jvasilakes/mito/pics/1000009353.jpg

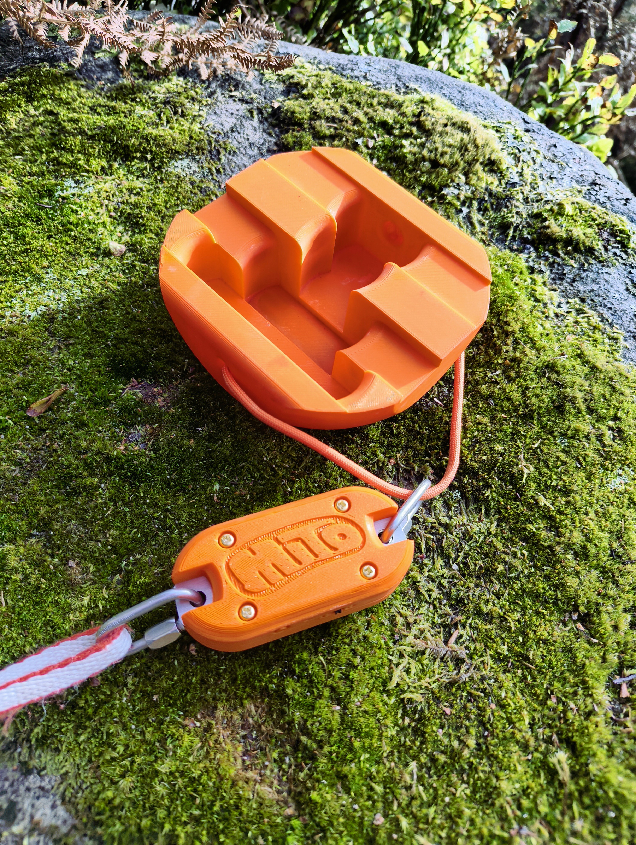
pics/1000009353.jpg
