jvasilakes/mito/pics/1000009354.jpg

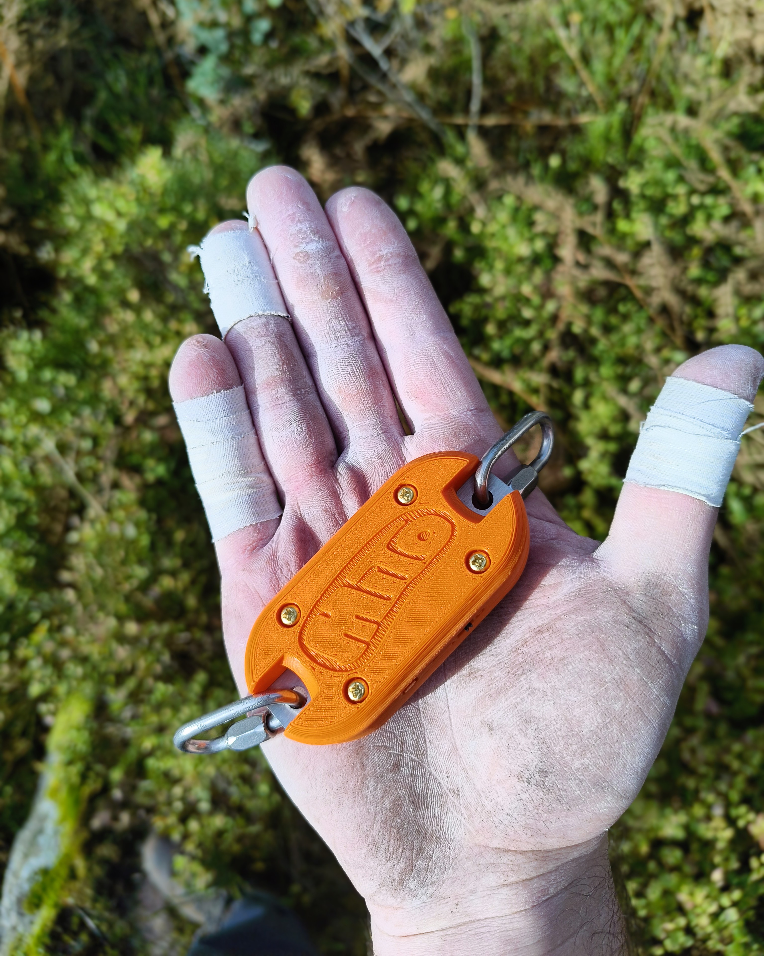
pics/1000009354.jpg
