jvasilakes/mito/pics/1000009355.png

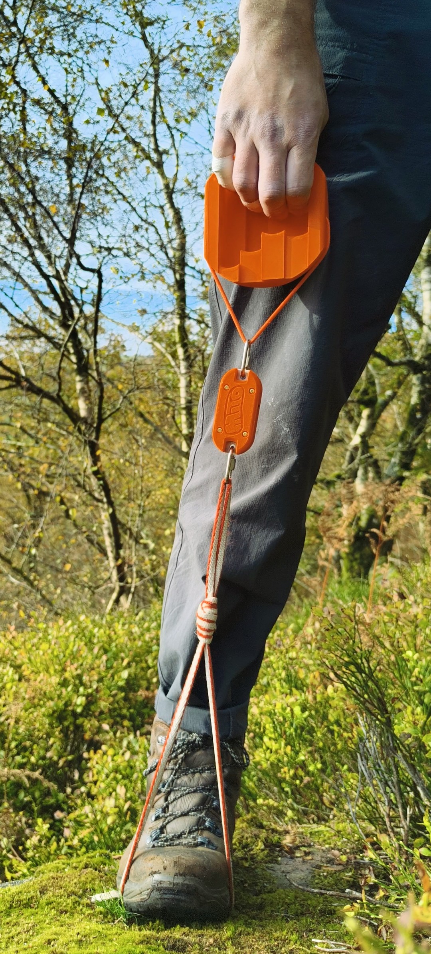
pics/1000009355.png
