jvasilakes/mito/hardware/enclosure/enclosure_bottom_with_window.3mf

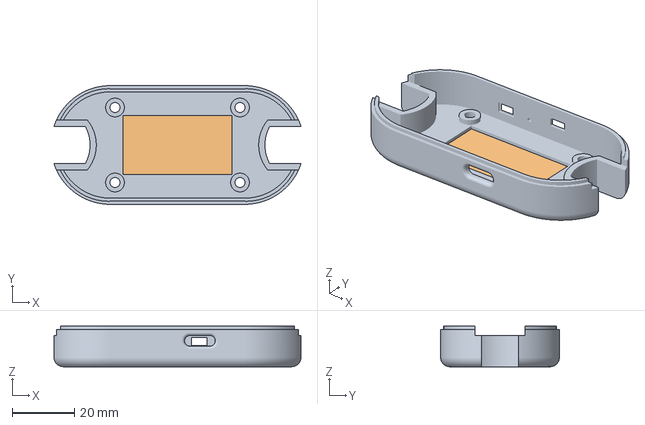
[picture p23: CAD file, 2025-10-13]
hardware/enclosure/enclosure_bottom_with_window.3mf
79.1 x 38.0 x 13.0 mm
enclosure2-Bottom_with_window.step
enclosure2-Bottom_window.step
