jvasilakes/mito/hardware/enclosure/enclosure2-Bottom_window.step

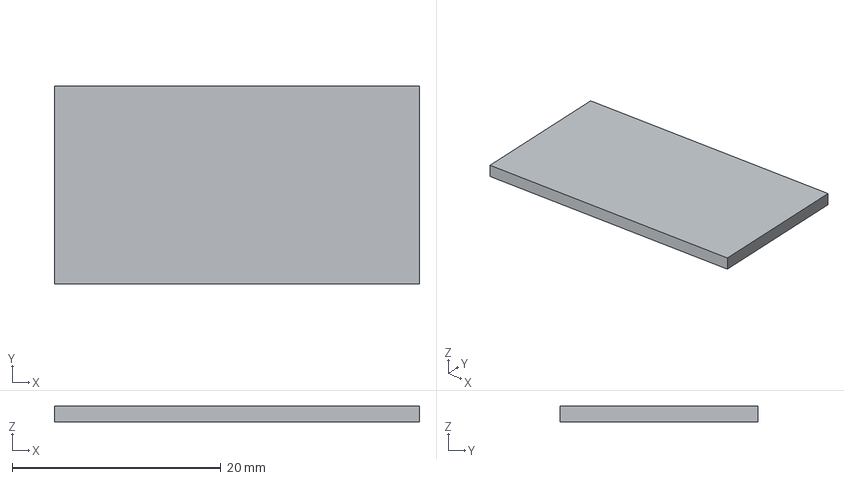
[picture p24: CAD file, 2025-10-13]
hardware/enclosure/enclosure2-Bottom_window.step
35.0 x 19.0 x 1.50 mm
