jvasilakes/mito/hardware/enclosure/enclosure2-Bottom_with_window.step

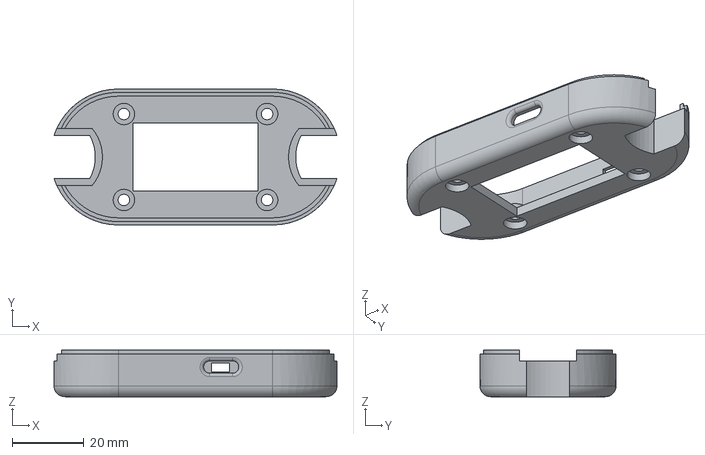
[picture p25: CAD file, 2025-10-13]
hardware/enclosure/enclosure2-Bottom_with_window.step
79.1 x 38.0 x 13.0 mm
