jvasilakes/mito/hardware/enclosure/transparent_test.3mf

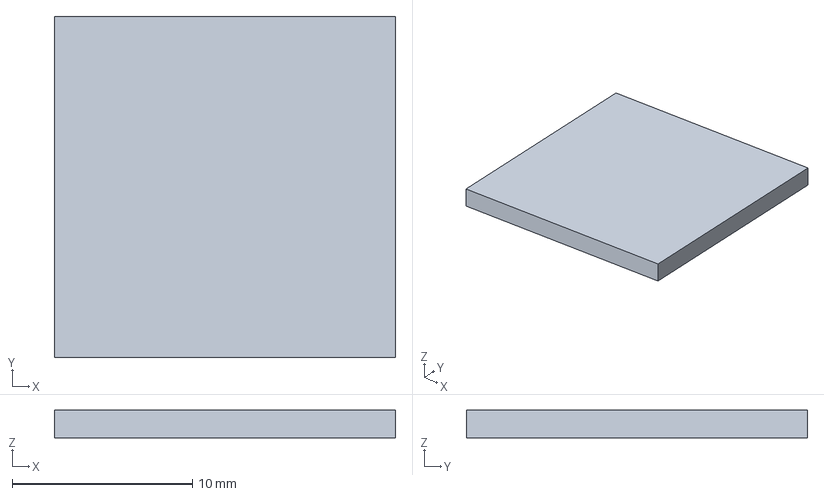
[picture p26: CAD file, 2025-10-13]
hardware/enclosure/transparent_test.3mf
18.9 x 18.9 x 1.53 mm
