jvasilakes/mito/hardware/enclosure/enclosure.FCStd

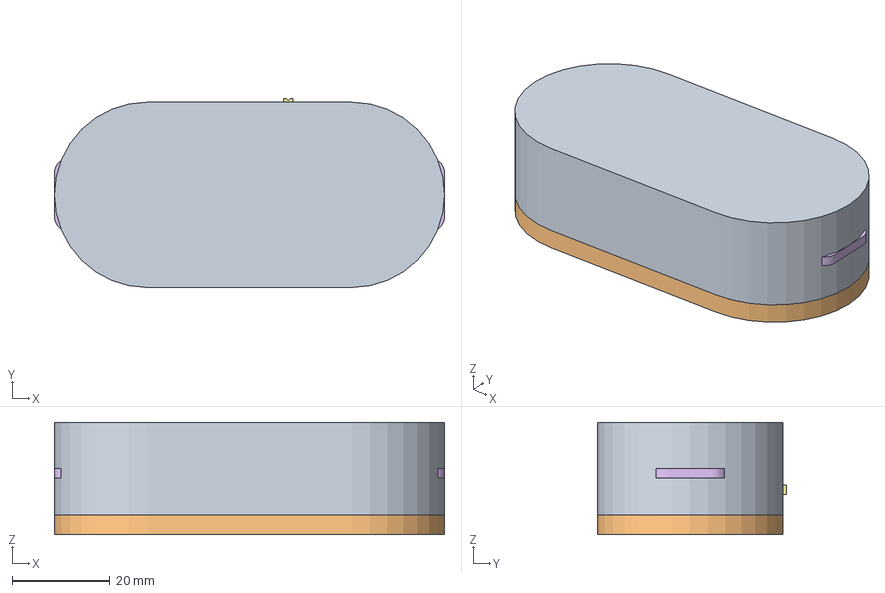
[picture p27: CAD file, 2025-09-03]
hardware/enclosure/enclosure.FCStd
80.0 x 38.7 x 23.0 mm
Top
Bottom
R_0603
R_0604
R_0605
C_0603
LED-ARRAY-SMD_4P-L3.2-W1.5-H1.0
LED-ARRAY-SMD_4P-L3.2-W1.5-H1.001
C_0604
C_0605
R_0606
SOIC-16_3.9x9.9mm_P1.27mm
R_0607
L_0805
C_0606
Pocket008_(Mirror_#2)
Pad007_(Mirror_#3)
Pad007_(Mirror_#5)
Pad007_(Mirror_#4)
R_0608
R_0609
C_0607
C_0608
BOSS-EXTRUDE14_8_
BOSS-EXTRUDE7_4_
BOSS-EXTRUDE7_3_
BOSS-EXTRUDE14_4_
BOSS-EXTRUDE14_2_
BOSS-EXTRUDE14_11_
BOSS-EXTRUDE7_7_
BOSS-EXTRUDE14_9_
BOSS-EXTRUDE14_3_
BOSS-EXTRUDE14_7_
MIRROR2
BOSS-EXTRUDE14_5_
BOSS-EXTRUDE14_12_
BOSS-EXTRUDE7_8_
BOSS-EXTRUDE7_1_
BOSS-EXTRUDE14_10_
BOSS-EXTRUDE7_9_
BOSS-EXTRUDE14_6_
BOSS-EXTRUDE14_1_
BOSS-EXTRUDE7_6_
BOSS-EXTRUDE7_2_
CUT-EXTRUDE5
BOSS-EXTRUDE7_5_
Shield
Pins
Pins001
Pins002
Pins003
CAP
CAP001
CAP002
ANT1
ANT002
ANT003
Silkscreen
Silkscreen001
Silkscreen002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
