jvasilakes/mito/hardware/enclosure/load_cell.stl

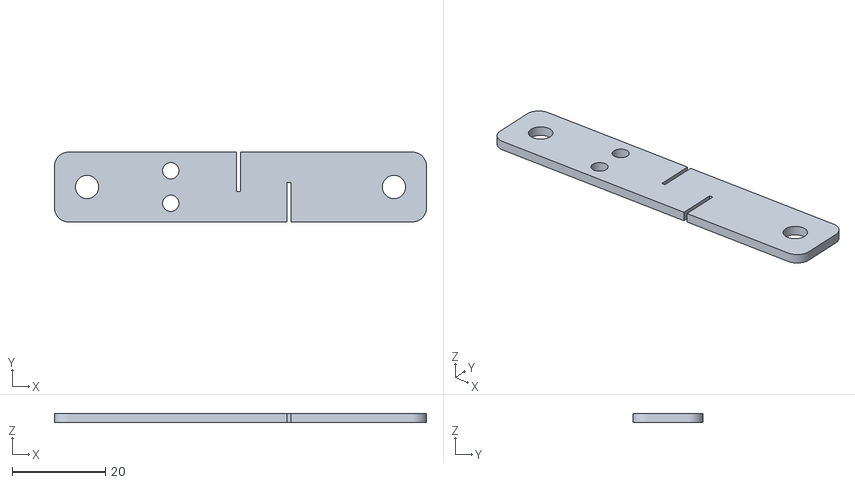
[picture p28: CAD file, 2025-08-31]
hardware/enclosure/load_cell.stl
80.0 x 15.0 x 2.00
